MichellNoLastName/ProyectoTT2_EEG/PCB/electrodo v1.jpg

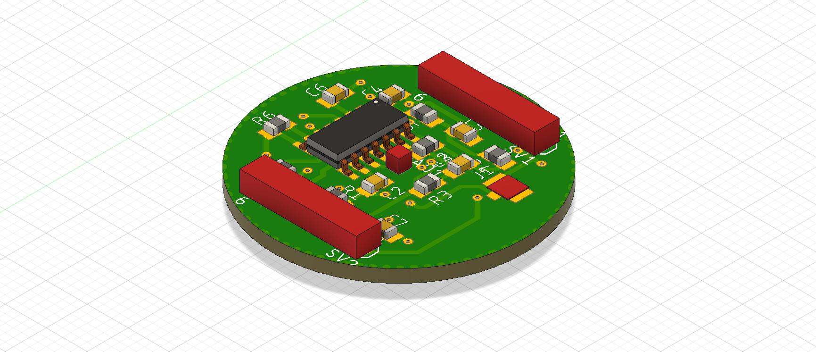
PCB/electrodo v1.jpg
