MichellNoLastName/ProyectoTT2_EEG/PCB/electrodoCircuit.png

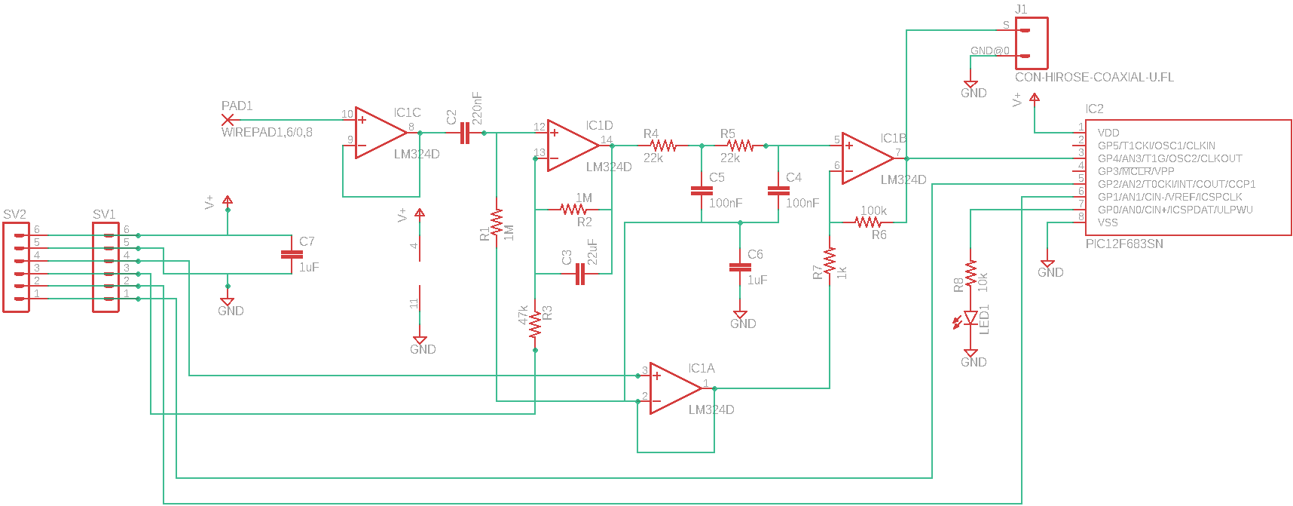
PCB/electrodoCircuit.png
