MichellNoLastName/ProyectoTT2_EEG/PCB/referenciaPCB.png

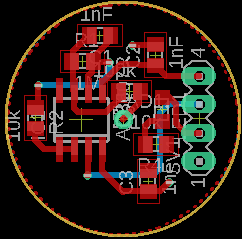
PCB/referenciaPCB.png
