MichellNoLastName/ProyectoTT2_EEG/PCB/tajeta.png

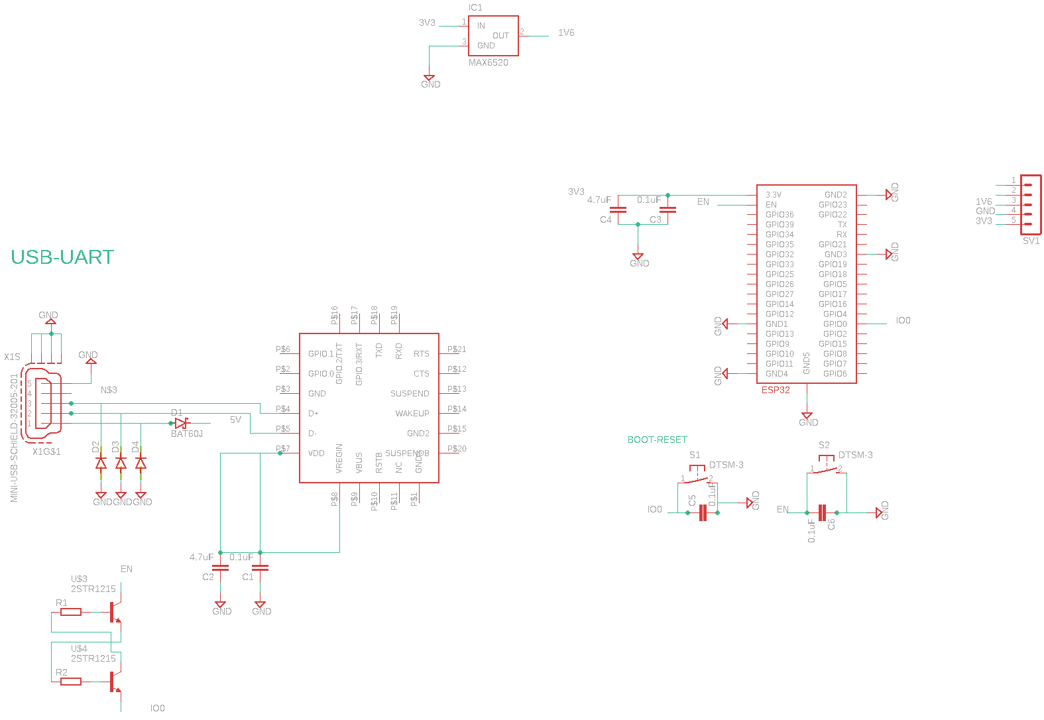
PCB/tajeta.png
